flora-comms/flora-hardware/pcb-references/hardware-overview.xlsx

Hardware Overview FLoRa Outdoor Communications Cameron Gillingham, Tella Osler, Aaron Huinink
Required Part | Proposed Component | Vendors | Unit cost | Link | Lifecycle status | Footprint | Justification
IC's
Microcontroller | ESP32-S3-MINI-1-N8 | JLC Parts - PN:C2913206 Mouser - PN:356-ESP32-S3-MINI1N8 Digi-key - PN:1965-ESP32-S3-MINI-1-N8TR-ND | $3.675 $4.50 $4.76 |  | Mass Production | Custom SMT | Settled on the ESP32-S3 due to its wifi capabilty and sleep functionaly in a cheap all in one package, There is also an abundance in documentation for developing porjects within the esp32 framework. Decided on the S# as it has plenty of Spare GPIO for future expansion and will need the extra power to support the web-app
LoRa Module | WAVE-20855-HF, Core1262 or Heltec ht-RA62 | waveshare.com - PN:20855 Abra Electronics Amazon.ca | $7.99 $15.95 $21.17 |  | Unknown | Custom SMT | This is a rare and expensive part, but will greatly speed up developent as it will reduce the complexity of the PCB design. For rev2.0 or further production we will dothe correct impedance matching to just use the raw sx1262 chip.
Voltage Regulator | RT9013-33GB | JLC Parts - PN:C7434207 Mouser - PN:835-RT9013-33GB Digi-key - PN:1028-RT9013-33GBTR-ND - Tape & Reel (TR) | $0.05 $0.856 $0.88 |  | No EOL notice plenty of availabliity | SOT-23-5 | ultra low voltage dropout of 250mV and quiescent current of 25uA make it a great choice for battery operation. 500 mA Ishigher than anything I could find with comparable dropout voltage.
Basic Components
Resistors | purpose dependent | ~ | ~ |  | ~ | 0604 SMT | Small footprint for compact design but still hand solderble if necessary to swap comonent values duting develeopment
Capacitors | pupose dependent | ~ | ~ |  | ~ | 0604 SMT | Small footprint for compact design but still hand solderble if necessary to swap comonent values duting develeopment
Inductors | purpose dependent | ~ | ~ |  | ~
LED | Red SMT 0805 led | Mouser - PN:710-150080RS75000 Digi-key - PN:L62501TR-ND - Tape & Reel (TR) | $0.28 $0.88 |  | ~ | 0805 SMT Reverse mount | Chose cheap and highly available red LED from mouser and digi-key
Button | 4 pin tact switch | Mouser - PN:611-PTS526SK15SMR2L Digi-key- PN:CKN12221-2-ND - Tape & Reel (TR) | $0.203 $0.21 |  |  | SMT | Cheap and widely avaiable, has footprint
NPN Transistors | General Purpose SMT Transistor | Mouser - PN:621-MMBT3904-F Digi-key - PN:MMBT2222ATPMSTR-ND - Tape & Reel (TR) | $0.145 $0.15 |  | ~ | SOT23 | Widely avaiable and cheap BJT transistor with a common footprint
Connectors
Solar Panel Connector | Solder connection | ~ | ~ |  | ~ | Through hole pads | For rev2.0 will purchase connectors but for rev1.0 will just solder to pads to save money
Battery Connecter | Solder connection | ~ | ~ |  | ~ | Through hole pads | For rev2.0 will purchase connectors but for rev1.0 will just solder to pads to save money
6 Pin programming header | THT pin headers | ~ | ~ |  | ~ | Through hole pads
Other
Batteries | Post PCB
Battert holders | Post PCB
Solar Panel W. incorporated charge controller | Post PCB
Antennas
Enclosures | Post PCB
Mounting hardware | Post PCB
SD Card Holder | Right angle SMT microSD | Digi-key - PN:2223-MSD-4-ATR-ND - Tape & Reel (TR) Mouser - PN:640-MEM20610118800A | $0.5 $1.74 |  | ~ | Custon SMT | Chose cheap and highly available SD card port from mouser and digi-key
Volatge Regulator Options | Mouser lInk | Digi Link
TPS78533QWDRBRQ1 | https://www.mouser.ca/ProductDetail/Texas-Instruments/TPS78533QWDRBRQ1?qs=iLbezkQI%252BsiNbdqh2Ko9GQ%3D%3D | https://www.digikey.ca/en/products/detail/texas-instruments/tps78533qwdrbrq1/14123967
LM1117MP-3.3/NOPB | https://www.mouser.ca/ProductDetail/Texas-Instruments/LM1117MP-3.3-NOPB?qs=X1J7HmVL2ZFn4x9DZ4T2hA%3D%3D | https://www.digikey.ca/en/products/detail/texas-instruments/LM1117MP-3-3-NOPB/304882
LDL1117S33R | https://www.mouser.ca/ProductDetail/STMicroelectronics/LDL1117S33R?qs=AQlKX63v8Rt9Bf6AWSrbFg%3D%3D | https://www.digikey.ca/en/products/detail/stmicroelectronics/LDL1117S33R/7102071
