flora-comms/flora-hardware/pcb-references/esp32-pin-map.xlsx

ESP32-C3-MINI-1 Pins
Name | No. | Type | Function | fLoRa Use | Notes
GND | 1,2,11,14,36-53 | P | Ground | GND | -
3V3 | 3 | P | Power Supply | 3V3 | -
NC | 4,7,9,10,15,17,24,25,28,29,32-35 | - | Not Connected | - | -
IO2 | 5 | I/O/T | GPIO2, ADC1_CH2, FSPIQ | Battery Voltage measurment | Through voltage divider for Appropriate ADC Range
IO3 | 6 | I/O/T | GPIO3, ADC1_CH3 | Indicator | bi-directional green/red
EN | 8 | I | HIGH: on, enable the chip Low: off, chip powers off Note: do not leave EN floating | EN | Pull high through 10K
IO0 | 12 | I/O/T | GPIO0, ADC1_CH0, XTAL_32K_P | SPI CS_1 | SPI Chip select for SD Card
IO1 | 13 | I/O/T | GPIO1, ADC1_CH1, XTAL_32K_N | SPI CS_2 | SPI Chip select for LoRa Module
IO10 | 16 | I/O/T | GPIO10, FSPICS0
IO4 | 18 | I/O/T | GPIO4, ADC1_CH4, FSPIHD, MTMS | SPI MISO | UNSURE of this pin
IO5 | 19 | I/O/T | GPIO5, ADC2_CH0, FSPIWP, MTDI
IO6 | 20 | I/O/T | GPIO6, FSPICLK, MTCK | SPI CLK
IO7 | 21 | I/O/T | GPIO7, FSPID, MTDO | SPI MOSI | UNSURE of this pin
IO8 | 22 | I/O/T | GPIO8 | Strapping Pin | Pull high through 10K, Maybe multi purpose?
IO9 | 23 | I/O/T | GPIO9 | Strapping Pin | to collector of boot transistor Q2, Maybe multi purpose?
IO18 | 26 | I/O/T | GPIO18, USB_D-
IO19 | 27 | I/O/T | GPIO19, USB_D+
RXD0 | 30 | I/O/T | GPIO20, U0RXD | U0RXD | From cp2102
TXDO | 31 | I/O/T | GPIO21, U0TXD | U0TXD | From cp2102
