flora-comms/flora-hardware/petal-v0_0/test-results/petal-current-measurement.xlsx

Petal Radio current measurements
Taken with EEVBLOG uCurrent Gold meter
 | Quiescent Current |  | Sleep Current |  | Active(web page open)
 | Vinput [V] | Qcurrent[uA] | Vinput [V] | Isupply[mA] | Vinput [V] | Isupply[mA]
 | 3.8 | 86 | 3.8 | 10.3 | 3.8
 | 5 | 96 | 5 | 8 | 5 | 90
 | 6 | 109 | 6 | 6.6 | 6 | 80
 | 7 | 126 | 7 | 5.8 | 7 | 67
 | 8 | 141 | 8 | 5 | 8 | 59
 | 9 | 155 | 9 | 4.5 | 9 | 53
 | 10 | 166 | 10 | 4.1 | 10 | 48
 | 11 | 182 | 11 | 3.7 | 11 | 44
 | 12 | 196.1 | 12 | 3.5 | 12 | 40.8
 | 13 | 209 | 13 | 3.2 | 13 | 38
 | 14 | 223.8 | 14 | 3 | 14 | 35.2
 | 15 | 238 | 15 | 2.8 | 15 | 33
 | 16 | 252 | 16 | 2.7 | 16 | 31
 | 17 | 266 | 17 | 2.5 | 17 | 29
 | 18 | 282 | 18 | 2.4 | 18 | 28
 | 19 | 295 | 19 | 2.3 | 19 | 26
 | 20 | 310 | 20 | 2.2 | 20 | 25.4
 | 21 | 324 | 21 | 2.1 | 21 | 24.3
 | 22 | 338 | 22 | 2.1 | 22 | 23.55
 | 23 | 353 | 23 | 2 | 23 | 23.2
 | 24 | 367 | 24 | 2 | 24 | 21.6
 | 25 | 382 | 25 | 1.9 | 25 | 21.4
 | 26 | 397 | 26 | 1.9 | 26 | 20.7
 | 27 | 411 | 27 | 1.8 | 27 | 19.5
 | 28 | 426 | 28 | 1.8 | 28 | 19
