flora-comms/flora-hardware/petal-v0_0/test-results/radio-testing/filtered_results.csv

 | Frequency (MHz) | Cheap | Mid | Expensive
0 | 900 | 1.559155295592745 | 1.4416397052216505 | 1.4657807548904043
1 | 901 | 1.5924831568393139 | 1.384069723248472 | 1.3870445787226935
2 | 902 | 1.624342942882127 | 1.3411570745840267 | 1.3251876944039764
3 | 903 | 1.6520530101989515 | 1.3242818227403097 | 1.289292598556054
4 | 904 | 1.6708347451952978 | 1.337957569115025 | 1.2774839372651965
5 | 905 | 1.6752744789826413 | 1.3783897614717857 | 1.279845034426417
6 | 906 | 1.6617329472768287 | 1.434027403331103 | 1.285169962093445
7 | 907 | 1.6310492686229185 | 1.488512810141992 | 1.2872519995384992
8 | 908 | 1.5903035199909408 | 1.5257127966988195 | 1.286986969265644
9 | 909 | 1.5519251528978366 | 1.5353585357655444 | 1.2895367448665451
10 | 910 | 1.530075654624506 | 1.5172182461072274 | 1.2993842522227201
11 | 911 | 1.5364344556950063 | 1.48178950838441 | 1.3170906924585355
12 | 912 | 1.5774012903931618 | 1.446435271287044 | 1.3389713830815442
13 | 913 | 1.6529888693984376 | 1.4282271433930287 | 1.3581839217113891
14 | 914 | 1.7566691297601886 | 1.4369467788848593 | 1.3661534317544528
15 | 915 | 1.8755409884031498 | 1.4713131934298869 | 1.355251153111595
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
