flora-comms/flora-hardware/petal-v0_0/test-results/radio-testing/results.xlsx

Sheet: Sheet1
 |  | https://plotdigitizer.com/app |  |  |  |  |  | reflected power by antenna = power reflected by antenna [mW] - power reflected by test set[mW]
 |  |  |  |  |  |  |  | return loss (dB) = 10log(power reflected by antenna [mW]) - power reaching antenna [dBm]
Termination | 50 Ohm |  |  |  |  |  |  |  | Lilygo |  |  |  |  |  |  |  | Lynx |  |  |  |  |  |  |  | Rockland
 | Frequency (MHz) | Power (-dBm) |  | Average | Std Dev | Return Loss (dB) | VSWR |  | Frequency (MHz) | Power (-dBm) |  |  | Average | Std Dev | Return Loss (dB) | VSWR | Frequency (MHz) | Power (-dBm) |  |  | Average | Std Dev | Return Loss (dB) | VSWR | Frequency (MHz) | Power (-dBm) |  |  | Average | Std Dev | Return Loss (dB) | VSWR
 | 900 | -13.24752475 | -10.85487078 | -12.05119776 | 1.691861852 |  |  |  | 900 | -10.14604462 | -9.756097561 | -11.49797571 | -10.46670596 | 0.9141403839 | -13.22229205 | 1.558249422 | 900 | -10.7611336 | -10.9979716 | -10.95874822 | -10.90595114 | 0.1269397816 | -14.86330859 | 1.44095509 | 900 | -8.462411348 | -11.58806818 | -12.38352273 | -10.81133409 | 2.072743473 | -14.46908847 | 1.466202119
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
